zouppen/pumpunjuksautin/juksutil/src/mmap.c

// Helper for mmap()
// SPDX-License-Identifier:   GPL-3.0-or-later
// Copyright (C) 2013-2021 Joel Lehtonen
//
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
#include <sys/types.h>
#include <sys/stat.h>
#include <fcntl.h>
#include <unistd.h>
#include <sys/mman.h>
#include <errno.h>
#include "mmap.h"

bool mmap_open(const char *pathname, mmap_mode_t mode, mmap_info_t *info)
{
	// Make the g_auto work correctly in case glib is used.
	info->data = NULL;

	int open_flags, mmap_prot, mmap_flags; // Flags depending on mode.

	// Determining options for open(2) and mmap(2).
	switch (mode) {
	case (MMAP_MODE_READONLY):
		open_flags = O_RDONLY;
		mmap_prot = PROT_READ;
		mmap_flags = MAP_PRIVATE;
		break;
	case (MMAP_MODE_WRITE):
		open_flags = O_RDWR;
		mmap_prot = PROT_READ | PROT_WRITE;
		mmap_flags = MAP_SHARED;
		break;
	case (MMAP_MODE_VOLATILE_WRITE):
		open_flags = O_RDONLY;
		mmap_prot = PROT_READ | PROT_WRITE;
		mmap_flags = MAP_PRIVATE;
		break;
	default:
		errno = EINVAL;
		goto fail_start;
	}

	// Opening a file as we do normally.
	info->fd = open(pathname, open_flags);
	if (info->fd == -1) goto fail_start;

	// Determining the length of this file.
	struct stat stats;
	if (fstat(info->fd, &stats) == -1) {
		goto fail_open;
	}
	info->length = stats.st_size;
	if (!S_ISREG(stats.st_mode)) {
		errno = ENOENT;
		goto fail_open;
	}

	// Doing some black bit magic with mmap.
	info->data = mmap(NULL, info->length, mmap_prot, mmap_flags, info->fd, 0);
	if (info->data == MAP_FAILED) goto fail_open;

	return info;
fail_open:
	close(info->fd);
fail_start:
	return false;
}

bool mmap_close(mmap_info_t *info)
{
	// If didn't even open the file
	if (info->data == NULL) return true;

	// Not processing failures. It is more important to close the
	// file. In that case close errno will overwrite this errno.
	munmap(info->data, info->length);

	// Close the file.
	return close(info->fd) != -1;
}
