zouppen/pumpunjuksautin/juksutil/src/sync_clock.h

#pragma once

#include <glib.h>

// Get time using Modbus
void sync_clock_get_time_modbus(GString *s, modbus_t *ctx);

// Synchronizes clock time of a device using Modbus
// protocol. Parameter real_time indicates if we synchronize current
// time or use supplied reference time.
void sync_clock_modbus(tzinfo_t const *tz, bool real_time, modbus_t *ctx);

// Synchronizes clock time of a device using the ASCII
// protocol. Parameter real_time indicates if we synchronize current
// time or use supplied reference time.
void sync_clock_ascii(tzinfo_t const *tz, bool real_time, FILE *f);
