zouppen/pumpunjuksautin/avr/src/pin.h

#pragma once

// MACROS FOR EASY PIN HANDLING FOR ATMEL GCC-AVR
// Copied from https://stackoverflow.com/a/25986570/514723

// These macros are used indirectly by other macros.
#define _SET(type,name,bit)          type ## name  |= _BV(bit)
#define _CLEAR(type,name,bit)        type ## name  &= ~ _BV(bit)
#define _TOGGLE(type,name,bit)       type ## name  ^= _BV(bit)
#define _GET(type,name,bit)          ((type ## name >> bit) &  1)
#define _PUT(type,name,bit,value)    type ## name = ( type ## name & ( ~ _BV(bit)) ) | ( ( 1 & (unsigned char)value ) << bit )

// These macros are used by end user.
#define OUTPUT(pin)         _SET(DDR,pin)
#define INPUT(pin)          _CLEAR(DDR,pin)
#define HIGH(pin)           _SET(PORT,pin)
#define LOW(pin)            _CLEAR(PORT,pin)
#define TOGGLE(pin)         _TOGGLE(PORT,pin)
#define READ(pin)           _GET(PIN,pin)
#define STATE(pin)          _GET(PORT,pin)
